John-A-Chen/Solid-Connections/Documentation/Diagrams/diagram-hero-render-red-enclosure.png

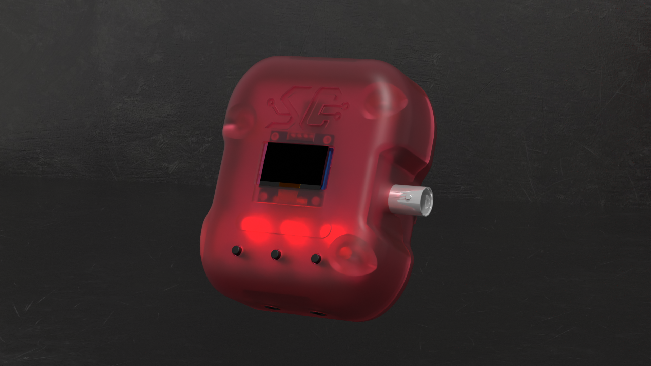
Documentation/Diagrams/diagram-hero-render-red-enclosure.png
