John-A-Chen/Solid-Connections/Documentation/Diagrams/diagram-system-block-v1.png

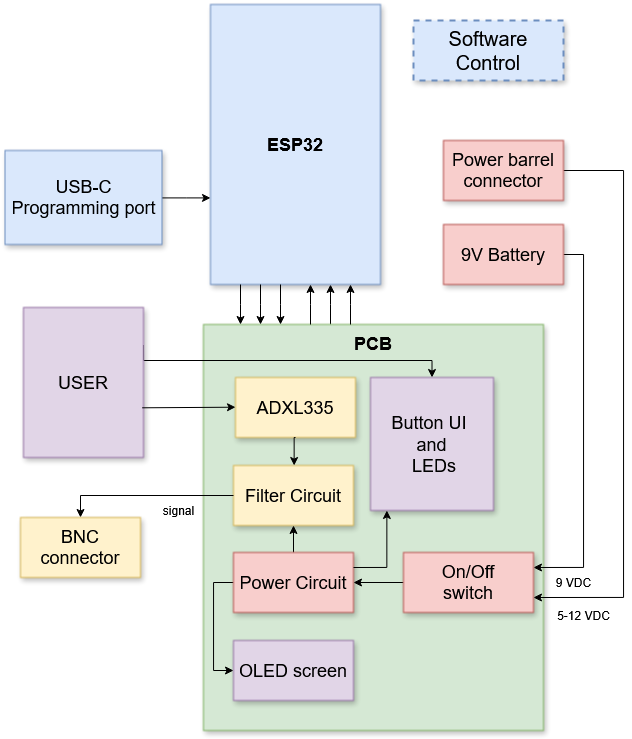
Documentation/Diagrams/diagram-system-block-v1.png
