John-A-Chen/Solid-Connections/Documentation/Images/flowchart-development-process.png

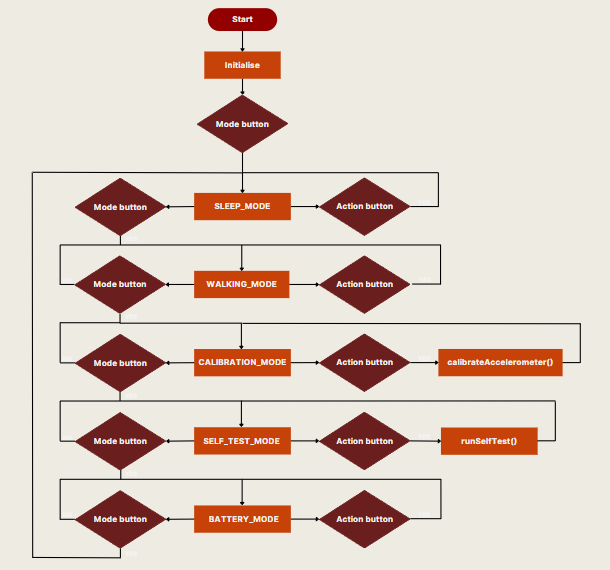
Documentation/Images/flowchart-development-process.png
