John-A-Chen/Solid-Connections/Documentation/Images/photo-device-in-hand-front-view-01.jpg

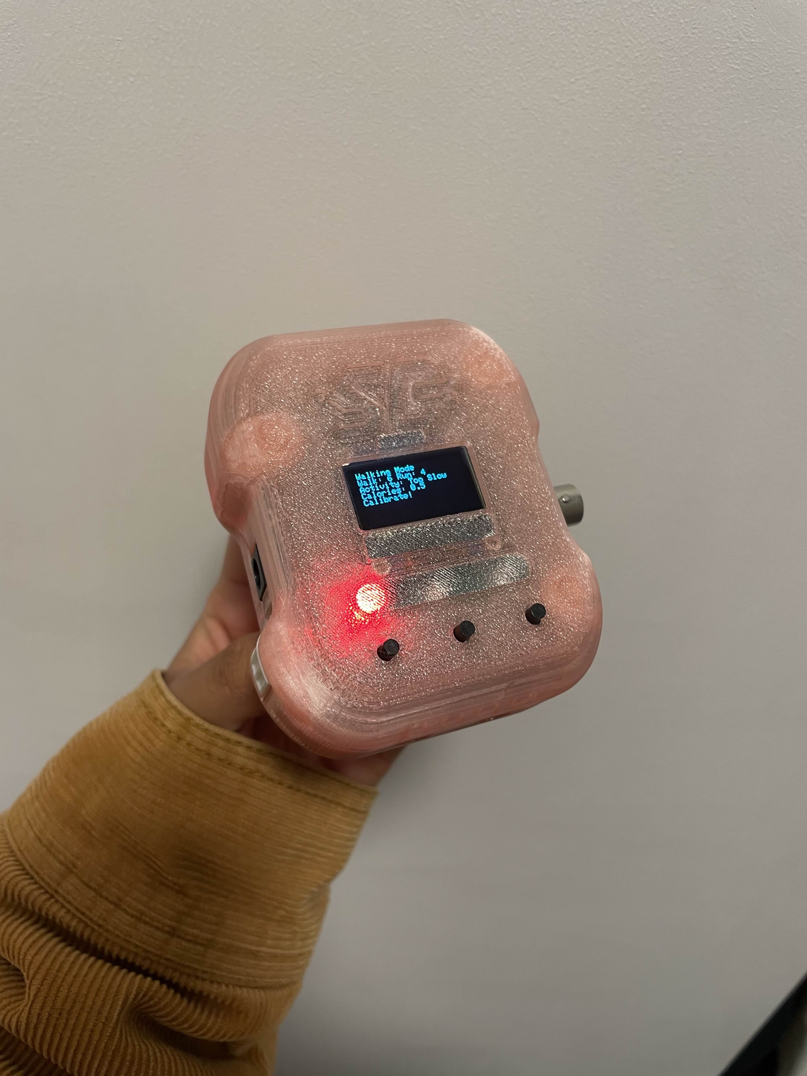
Documentation/Images/photo-device-in-hand-front-view-01.jpg
