John-A-Chen/Solid-Connections/Documentation/Images/photo-device-in-hand-front-view-03.jpg

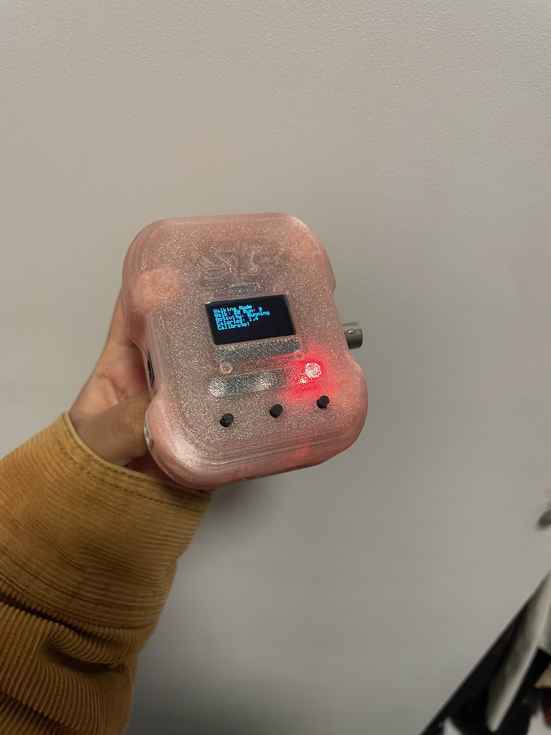
Documentation/Images/photo-device-in-hand-front-view-03.jpg
