John-A-Chen/Solid-Connections/Documentation/Images/photo-device-weight-on-scale.jpg

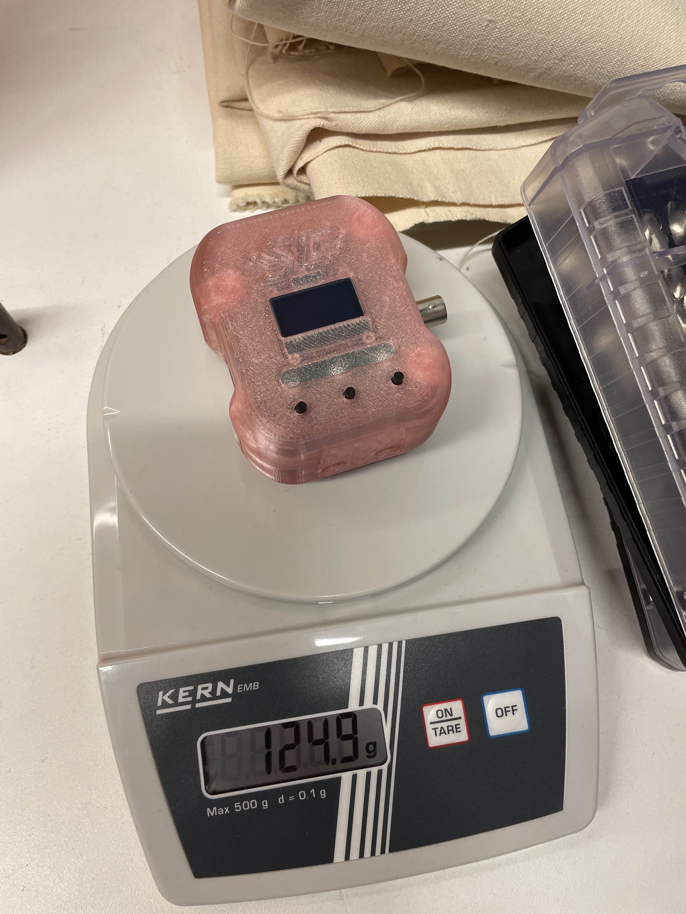
Documentation/Images/photo-device-weight-on-scale.jpg
