John-A-Chen/Solid-Connections/Documentation/Images/photo-device-worn-on-shirt.jpg

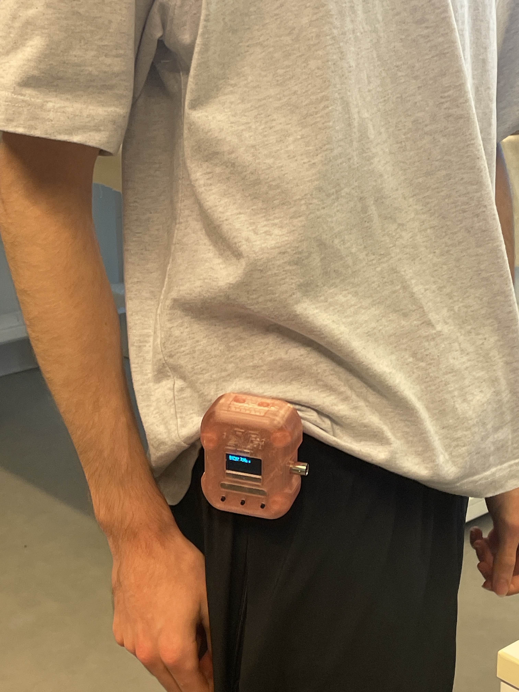
Documentation/Images/photo-device-worn-on-shirt.jpg
