John-A-Chen/Solid-Connections/Documentation/Images/photo-enclosure-front-angle-01.jpg

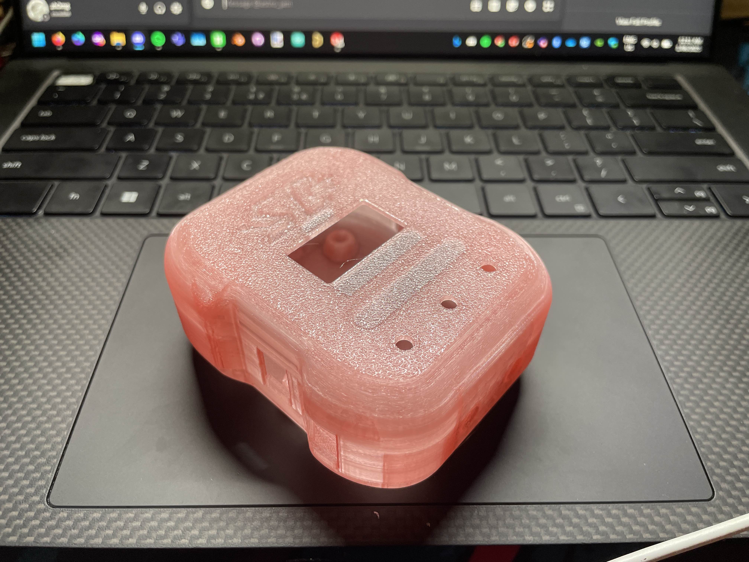
Documentation/Images/photo-enclosure-front-angle-01.jpg
