John-A-Chen/Solid-Connections/Documentation/Images/photo-enclosure-front-view-01.jpg

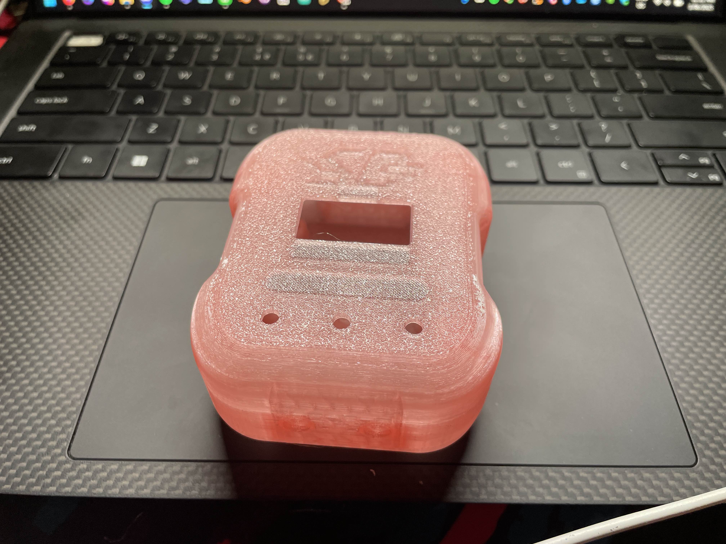
Documentation/Images/photo-enclosure-front-view-01.jpg
