John-A-Chen/Solid-Connections/Documentation/Images/photo-enclosure-side-view-01.jpg

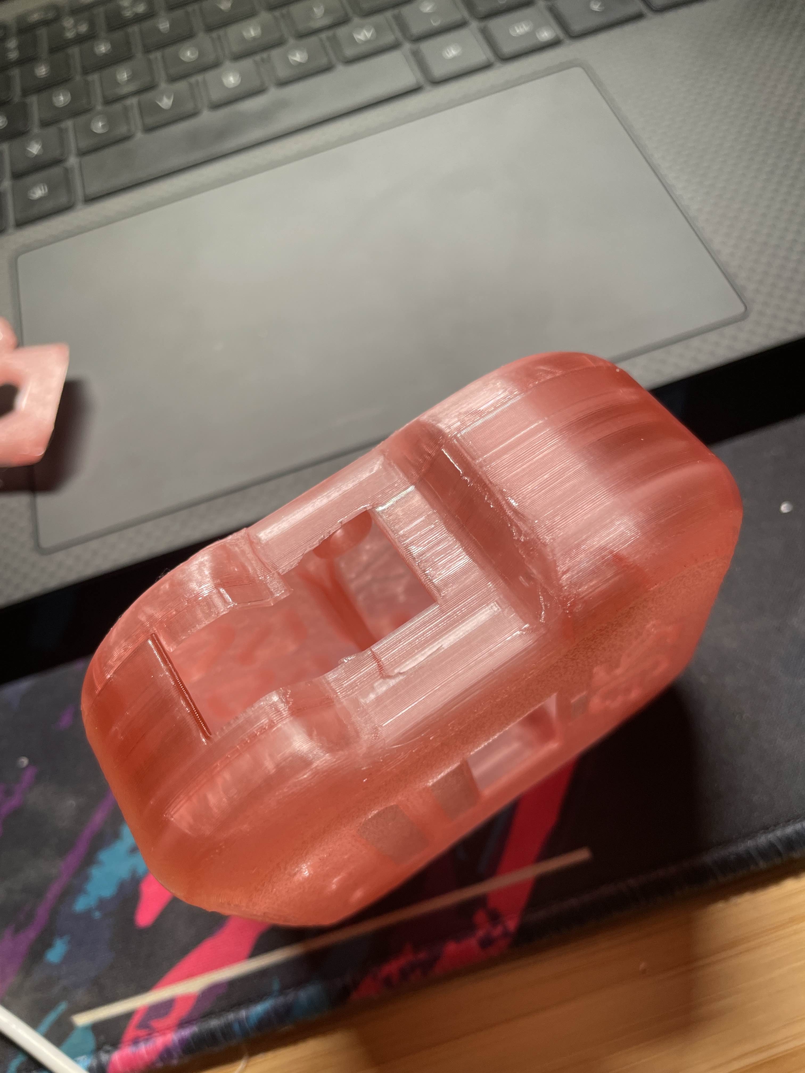
Documentation/Images/photo-enclosure-side-view-01.jpg
