John-A-Chen/Solid-Connections/Documentation/Images/photo-oled-module-on-desk.jpg

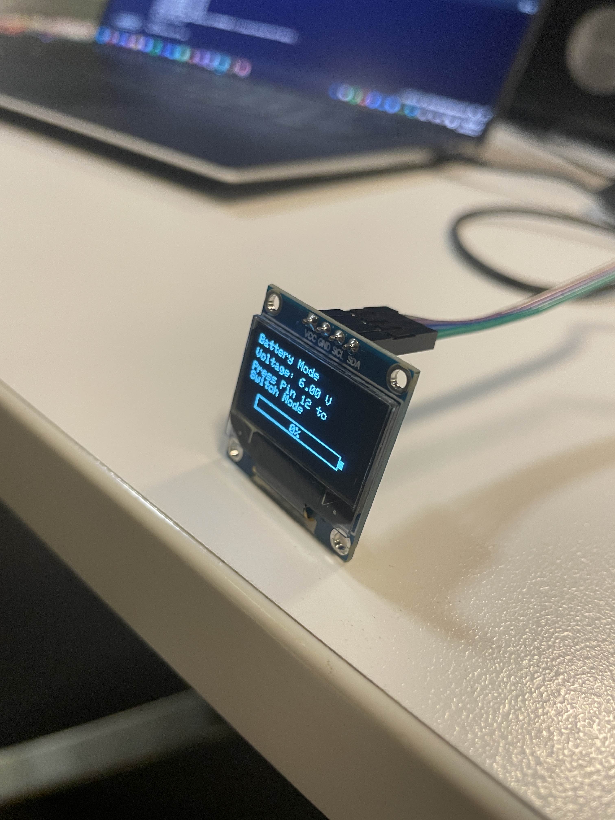
Documentation/Images/photo-oled-module-on-desk.jpg
