John-A-Chen/Solid-Connections/Documentation/Images/photo-pcb-and-oled-module-on-laptop.jpg

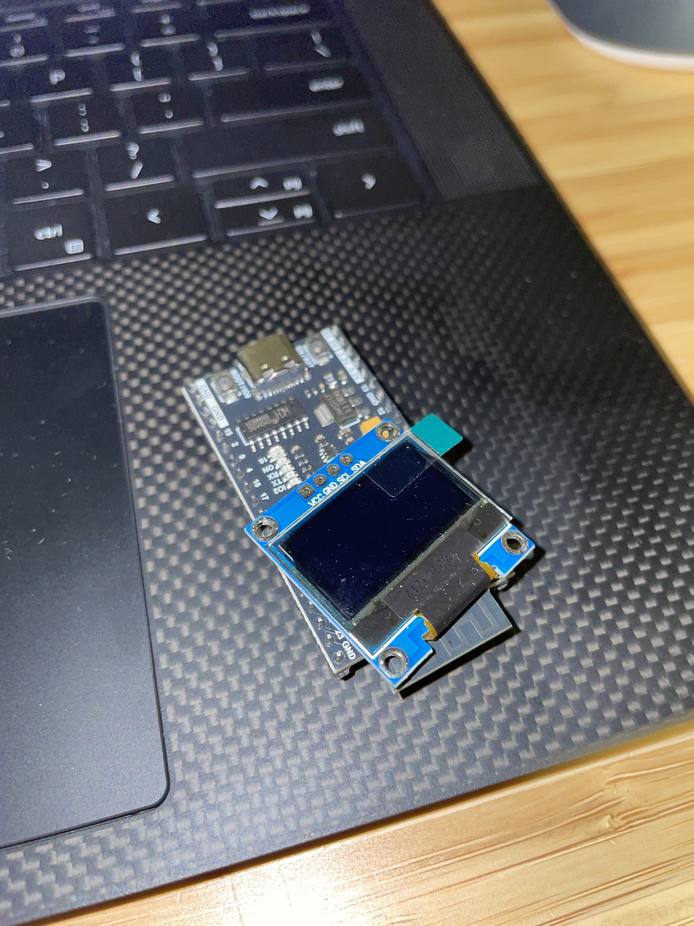
Documentation/Images/photo-pcb-and-oled-module-on-laptop.jpg
