John-A-Chen/Solid-Connections/Documentation/Images/photo-pcb-bare-back-view-01.jpg

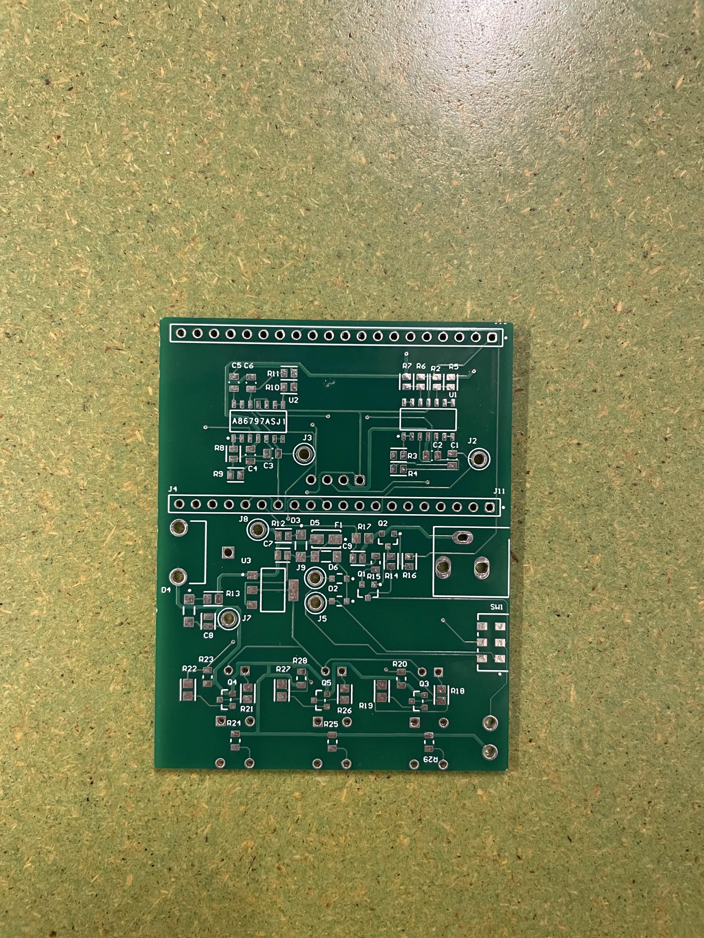
Documentation/Images/photo-pcb-bare-back-view-01.jpg
