John-A-Chen/Solid-Connections/Documentation/Images/photo-pcb-bare-back-view-02.jpg

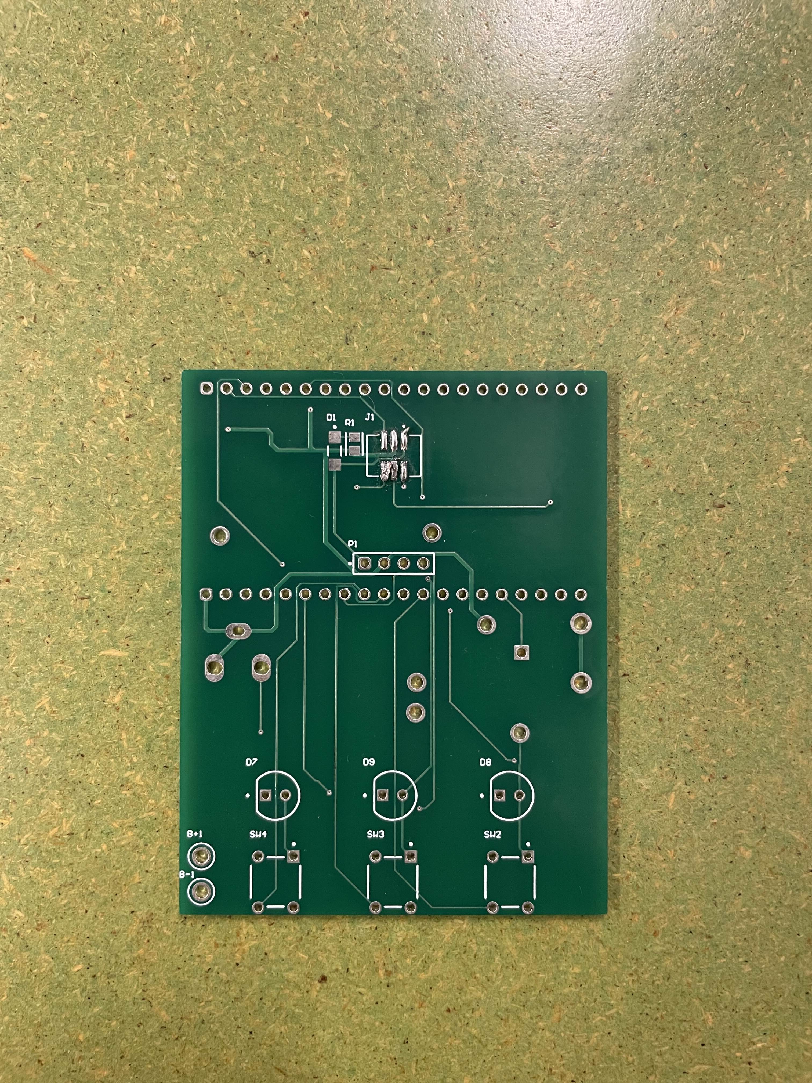
Documentation/Images/photo-pcb-bare-back-view-02.jpg
