John-A-Chen/Solid-Connections/Documentation/Images/photo-pcb-bare-front-view-01.jpg

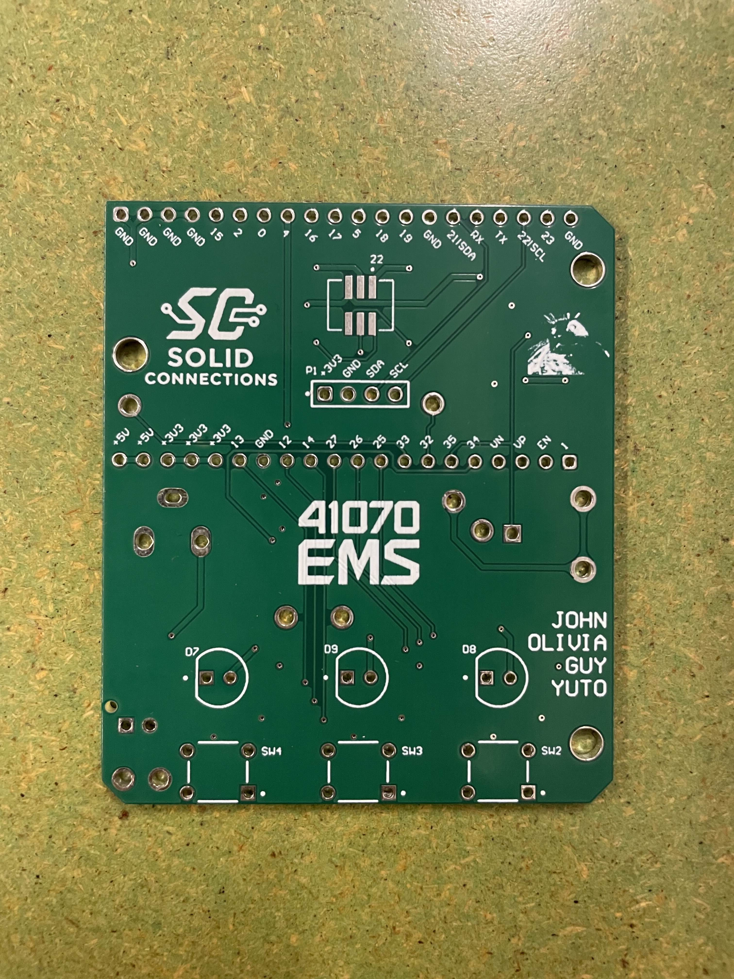
Documentation/Images/photo-pcb-bare-front-view-01.jpg
