John-A-Chen/Solid-Connections/Documentation/Images/photo-pcb-front-with-oled.jpg

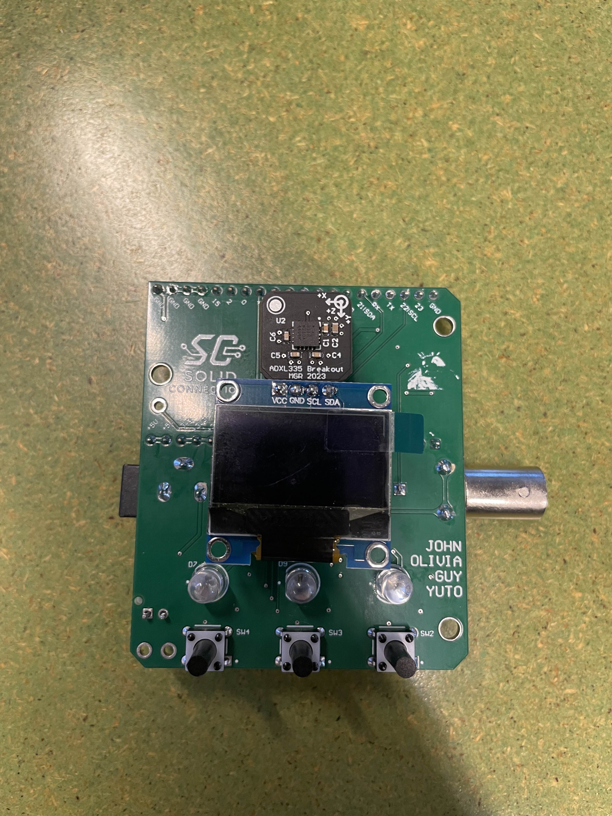
Documentation/Images/photo-pcb-front-with-oled.jpg
