John-A-Chen/Solid-Connections/Documentation/Images/photo-team-member-portrait-01.jpg

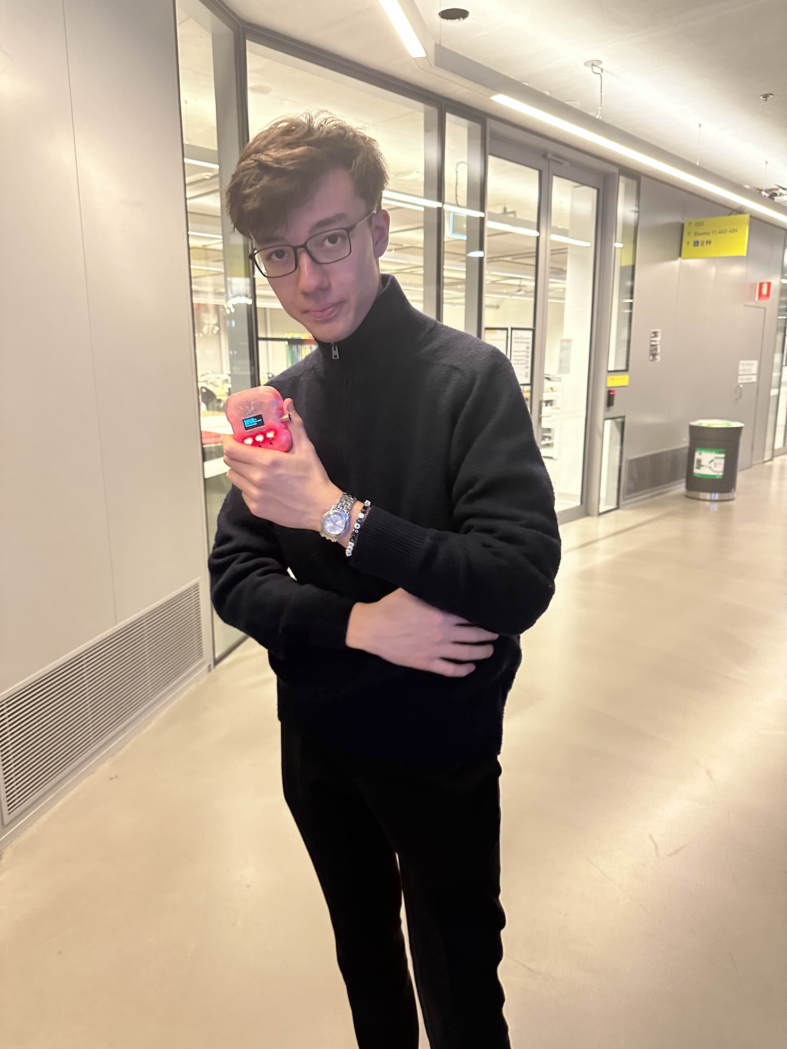
Documentation/Images/photo-team-member-portrait-01.jpg
