John-A-Chen/Solid-Connections/Documentation/Images/photo-team-member-portrait-02.jpg

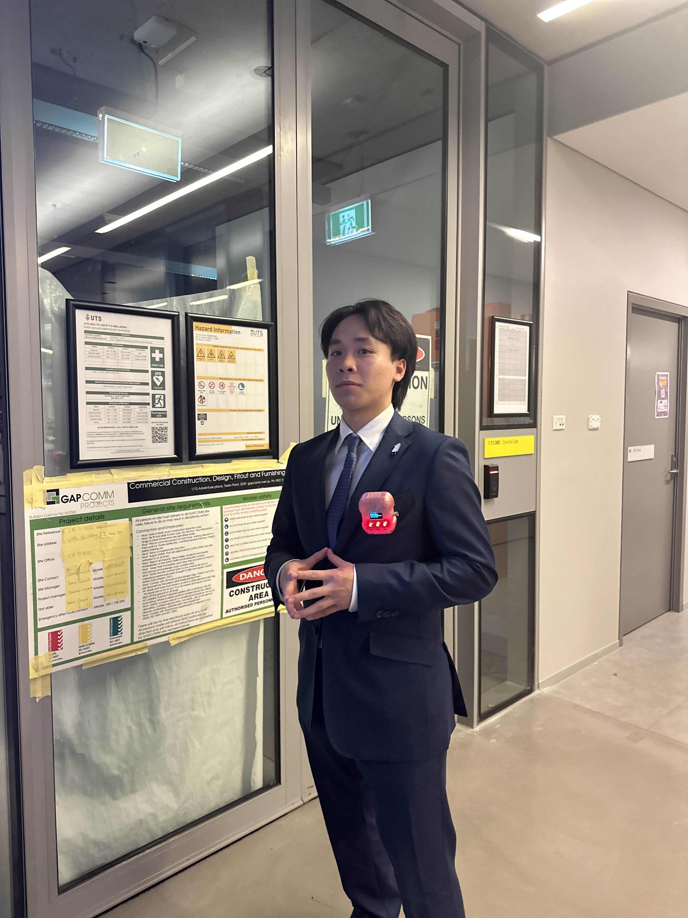
Documentation/Images/photo-team-member-portrait-02.jpg
