John-A-Chen/Solid-Connections/Documentation/Images/reference-tamagotchi-style.png

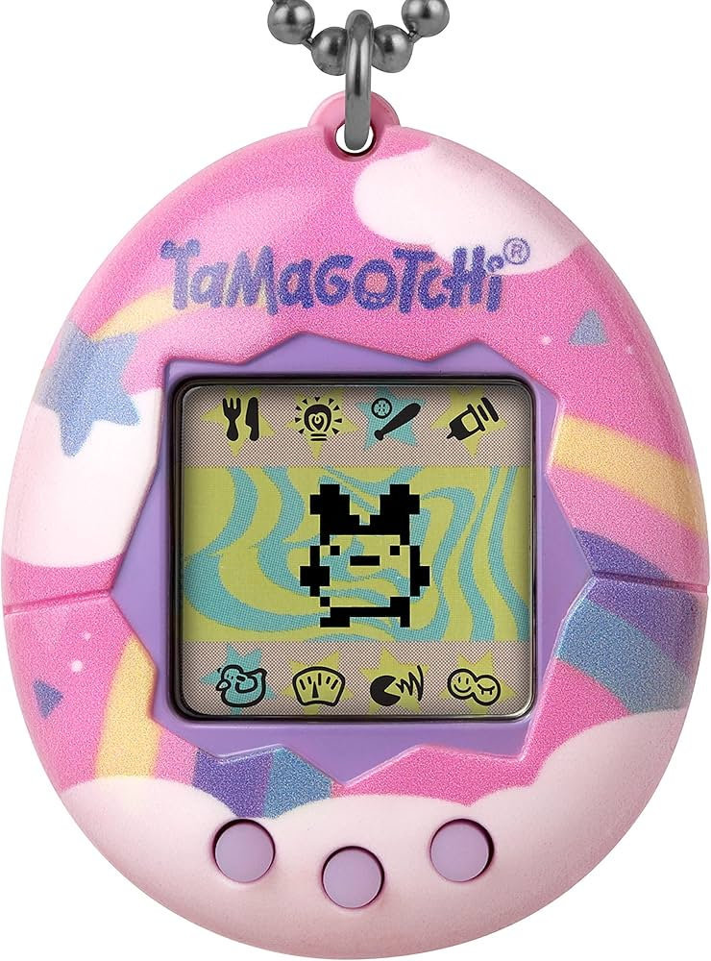
Documentation/Images/reference-tamagotchi-style.png
