John-A-Chen/Solid-Connections/Documentation/Images/render-enclosure-bottom-view.png

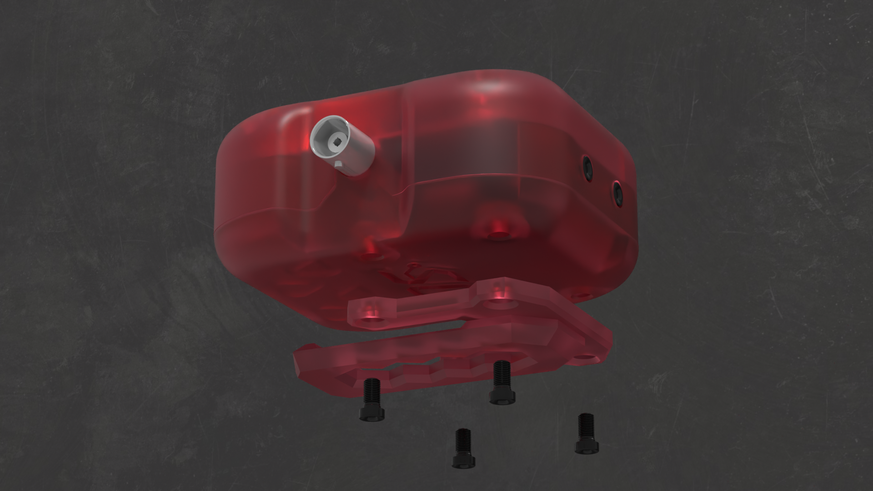
Documentation/Images/render-enclosure-bottom-view.png
