John-A-Chen/Solid-Connections/Documentation/Images/render-enclosure-open-with-pcb.png

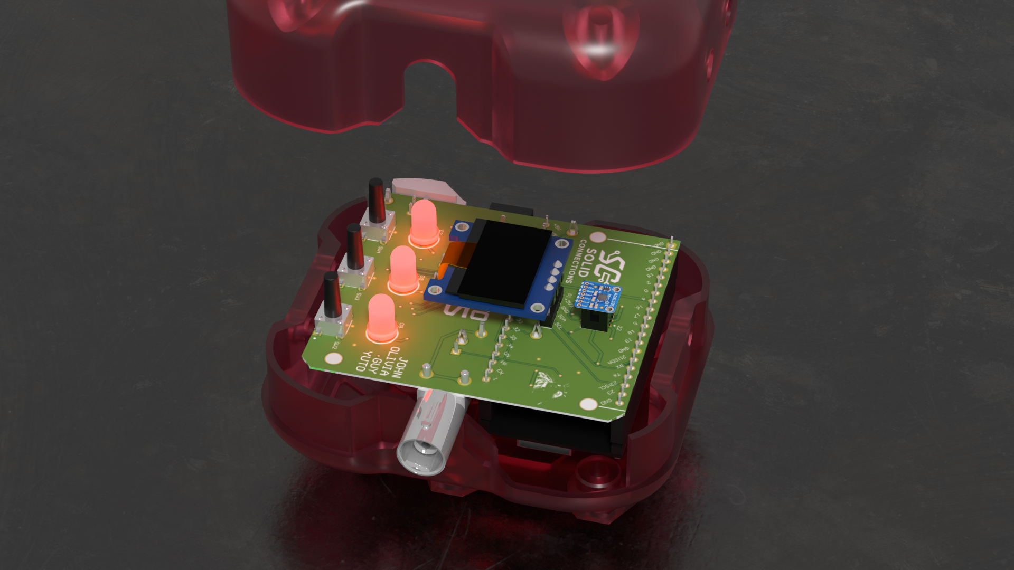
Documentation/Images/render-enclosure-open-with-pcb.png
