John-A-Chen/Solid-Connections/Documentation/Images/render-pcb-oled-closeup-01.png

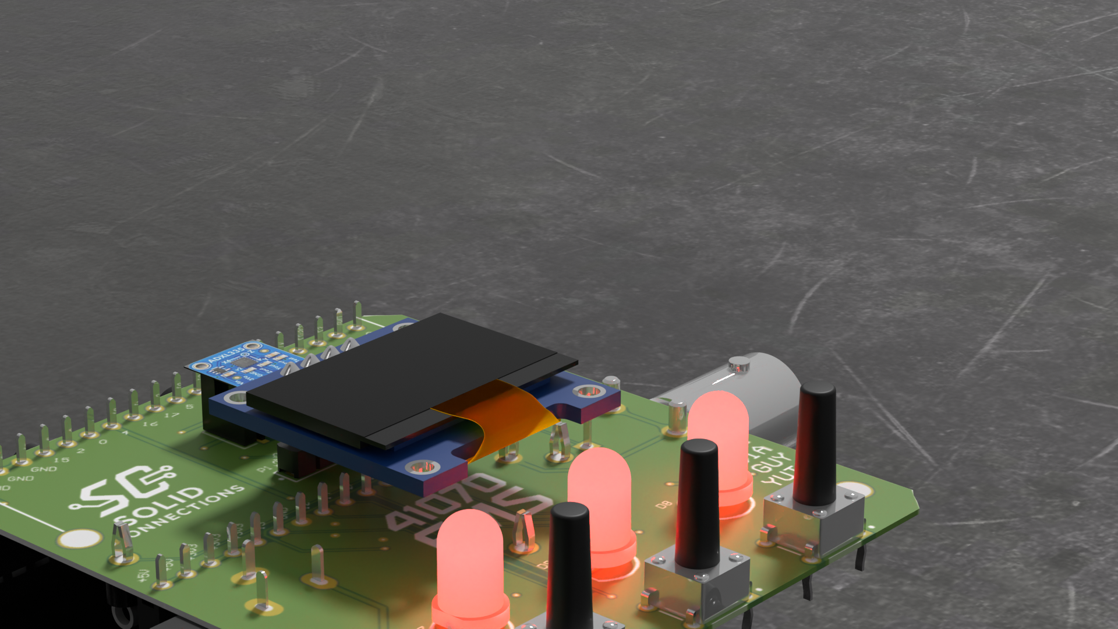
Documentation/Images/render-pcb-oled-closeup-01.png
