John-A-Chen/Solid-Connections/Documentation/Images/render-pcb-with-barrel-jack-angle-01.png

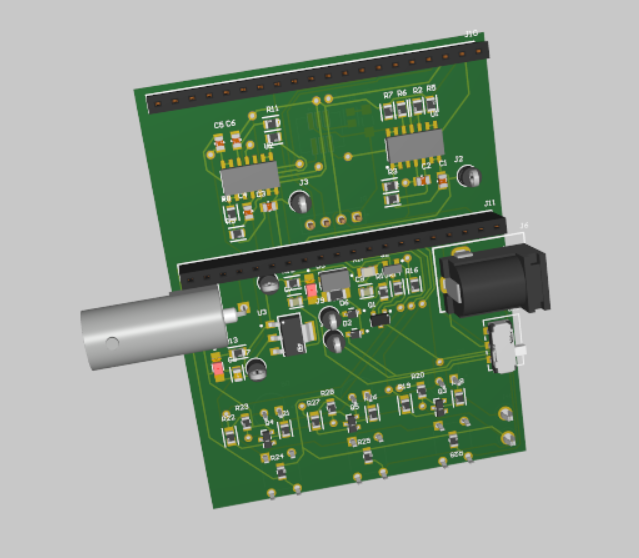
Documentation/Images/render-pcb-with-barrel-jack-angle-01.png
