John-A-Chen/Solid-Connections/Documentation/Images/render-pcb-with-controls-angle-02.png

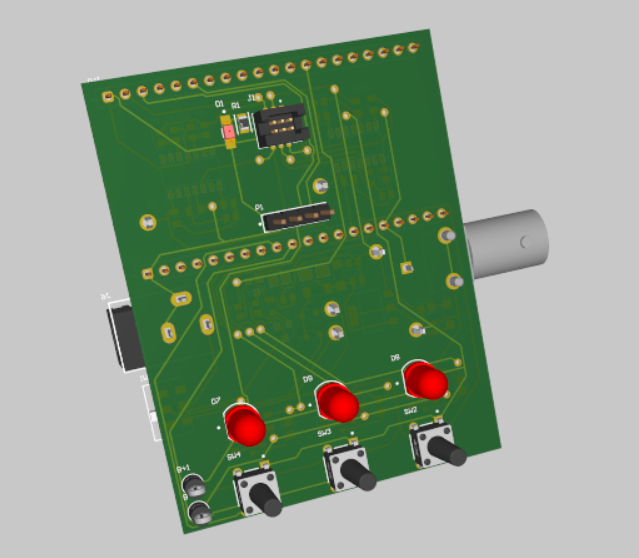
Documentation/Images/render-pcb-with-controls-angle-02.png
