John-A-Chen/Solid-Connections/Documentation/Images/render-purple-enclosure-front.png

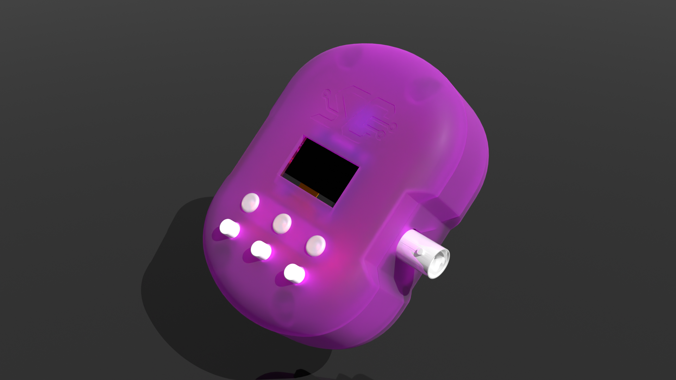
Documentation/Images/render-purple-enclosure-front.png
