John-A-Chen/Solid-Connections/Documentation/Images/render-side-stackup-view.png

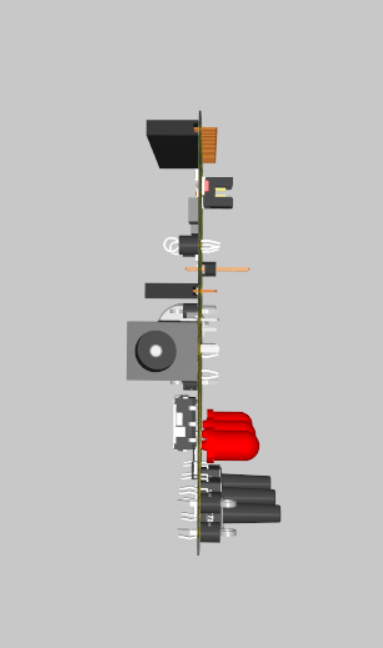
Documentation/Images/render-side-stackup-view.png
