John-A-Chen/Solid-Connections/Documentation/Images/render-technical-drawing-sheet.png

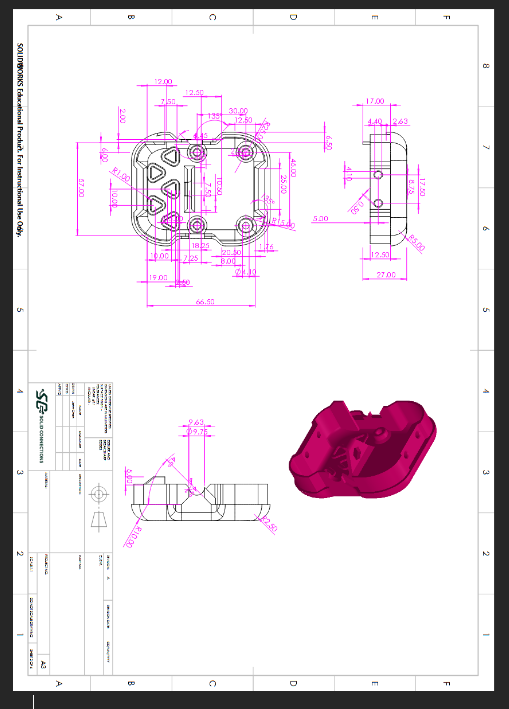
Documentation/Images/render-technical-drawing-sheet.png
