John-A-Chen/Solid-Connections/Documentation/Images/render-transparent-enclosure-cutaway-01.png

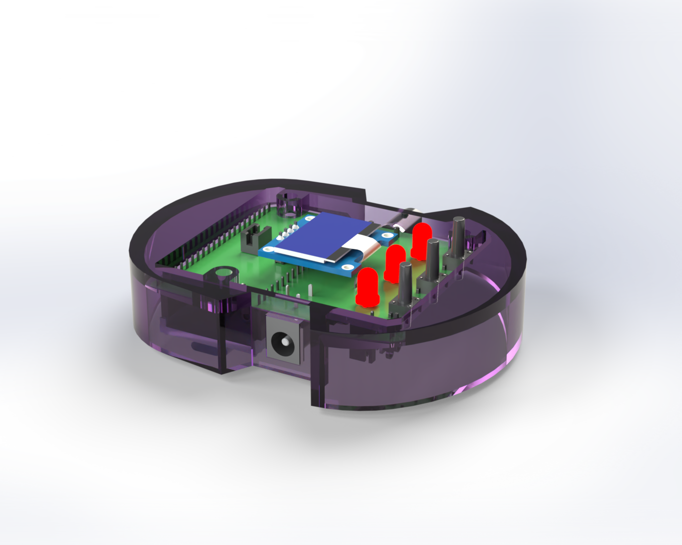
Documentation/Images/render-transparent-enclosure-cutaway-01.png
