John-A-Chen/Solid-Connections/Documentation/Images/render-transparent-enclosure-cutaway-02.png

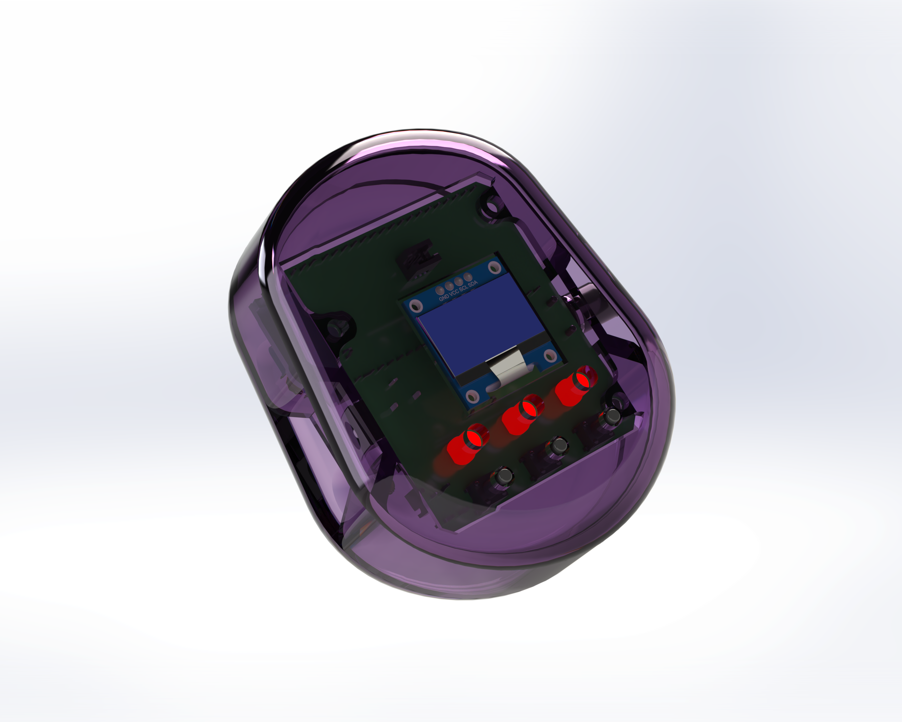
Documentation/Images/render-transparent-enclosure-cutaway-02.png
