John-A-Chen/Solid-Connections/Documentation/Images/photo-printed-parts-set-01.jpg

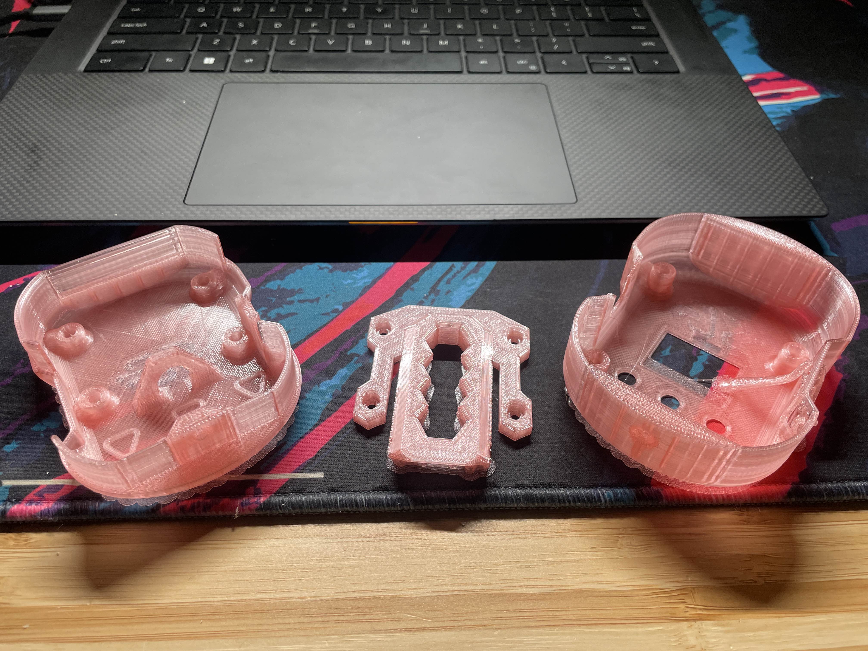
Documentation/Images/photo-printed-parts-set-01.jpg
