John-A-Chen/Solid-Connections/Documentation/Images/photo-printed-parts-set-02.jpg

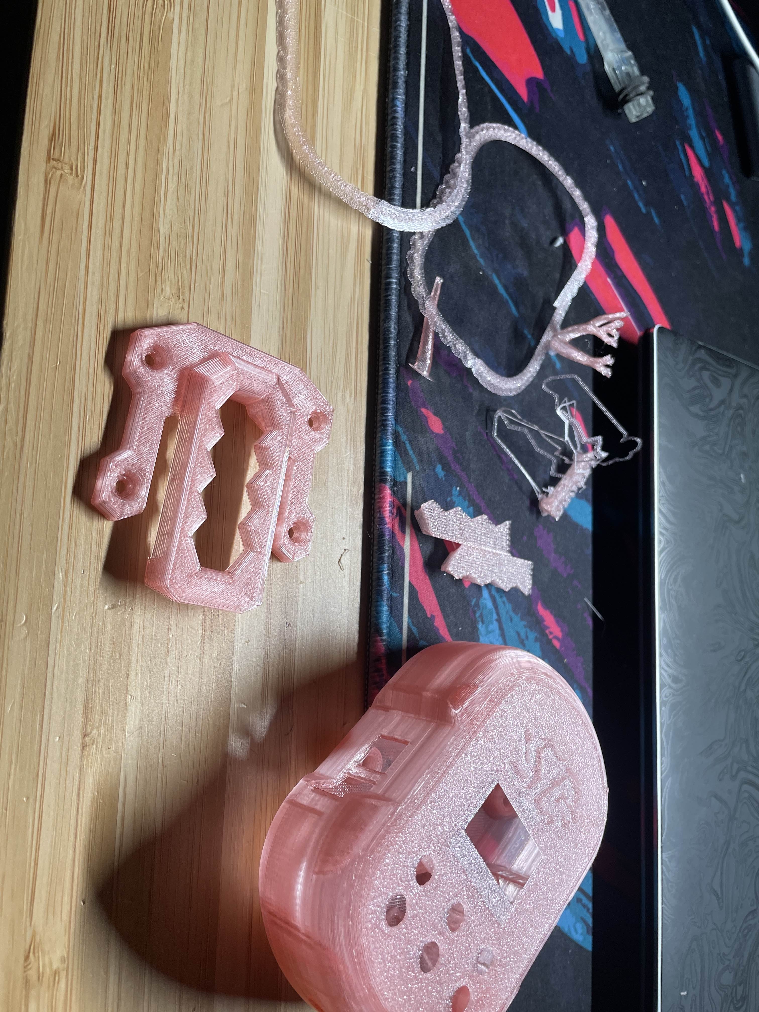
Documentation/Images/photo-printed-parts-set-02.jpg
