John-A-Chen/Solid-Connections/CAD/Assemblies/electronics package.SLDASM

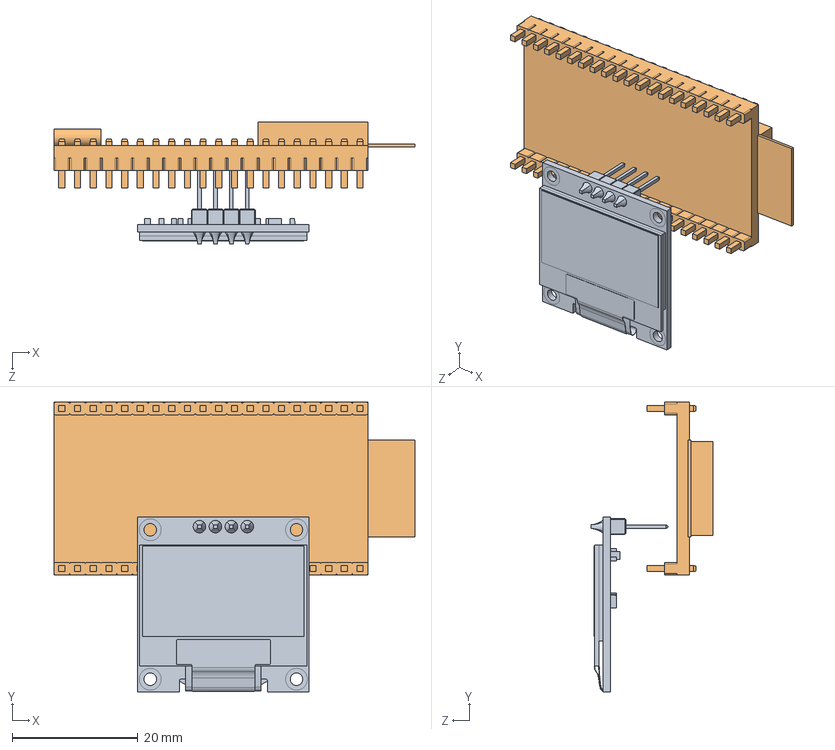
[picture p84: CAD file, 2026-03-31]
CAD/Assemblies/electronics package.SLDASM
57.5 x 46.1 x 19.5 mm
esp32
OLED TFT 0.96 inch 64x128 monochrome
