John-A-Chen/Solid-Connections/CAD/Print_Exports/clip2.3mf

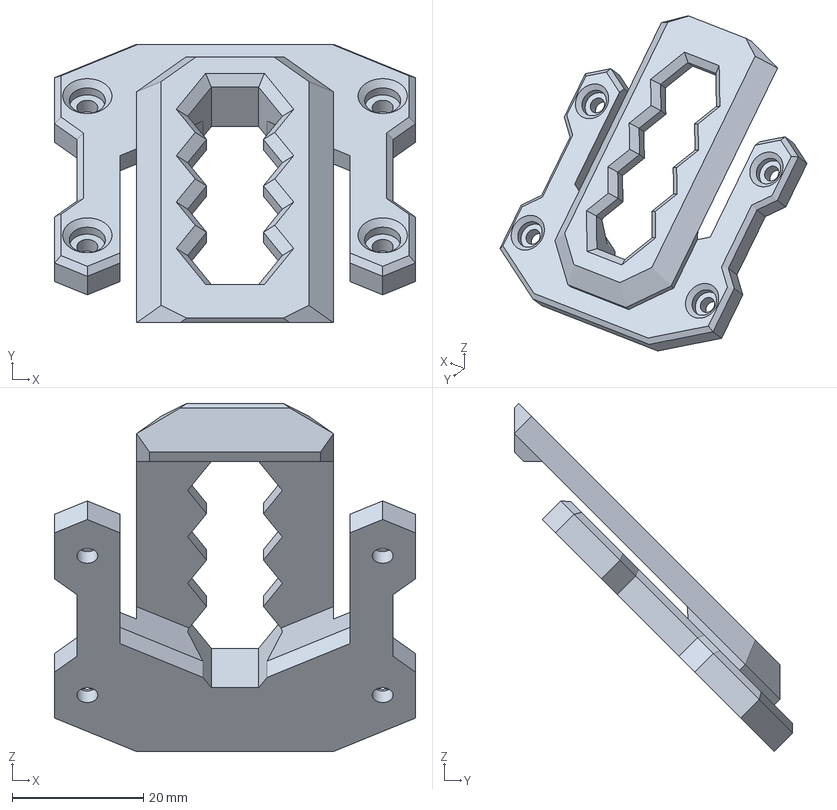
[picture p100: CAD file, 2026-02-22]
CAD/Print_Exports/clip2.3mf
55.0 x 42.4 x 53.0 mm
