John-A-Chen/Solid-Connections/Electronics/Reference_Models/esp32.SLDPRT

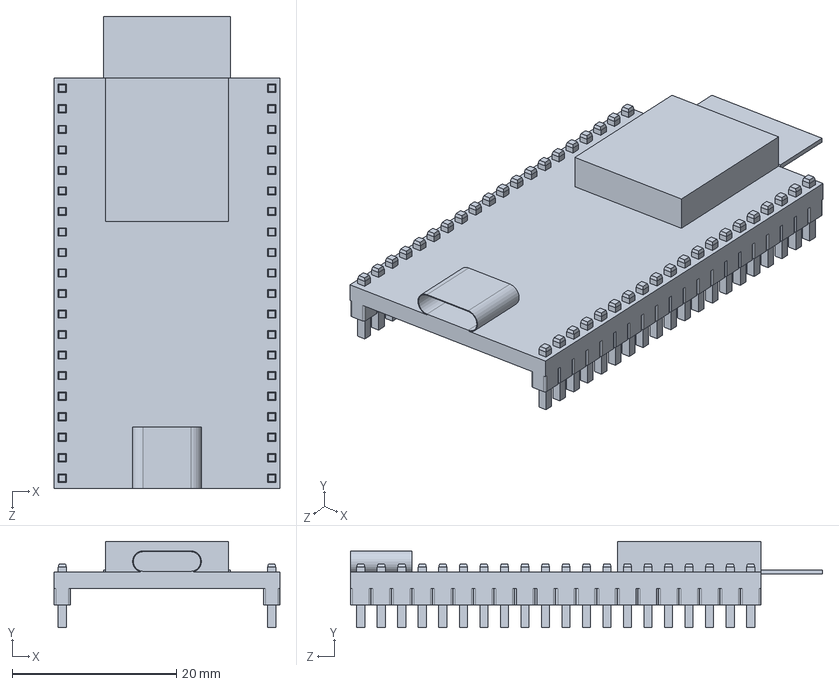
[picture p101: CAD file, 2026-02-22]
Electronics/Reference_Models/esp32.SLDPRT
27.5 x 10.5 x 57.5 mm
