John-A-Chen/Solid-Connections/CAD/Components/diffuser.STEP

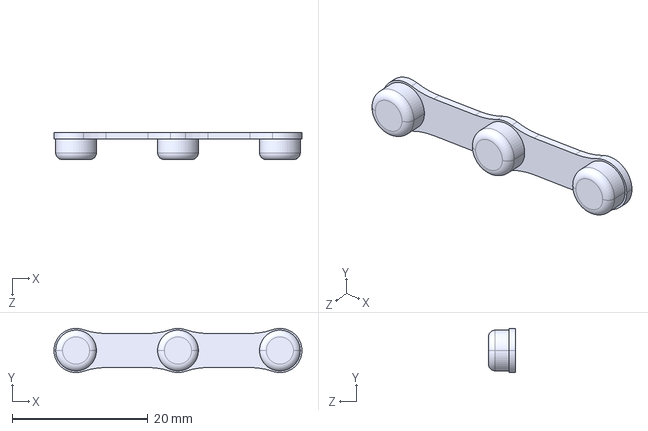
[picture p102: CAD file, 2026-02-22]
CAD/Components/diffuser.STEP
36.5 x 6.50 x 4.00 mm
