John-A-Chen/Solid-Connections/CAD/Print_Exports/switchcover2.3mf

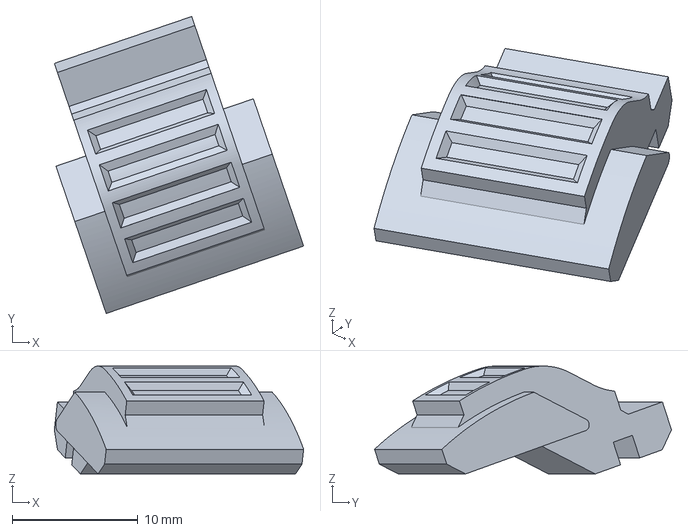
[picture p103: CAD file, 2026-02-22]
CAD/Print_Exports/switchcover2.3mf
19.8 x 23.6 x 8.58 mm
