John-A-Chen/Solid-Connections/CAD/Components/shellback6.STEP

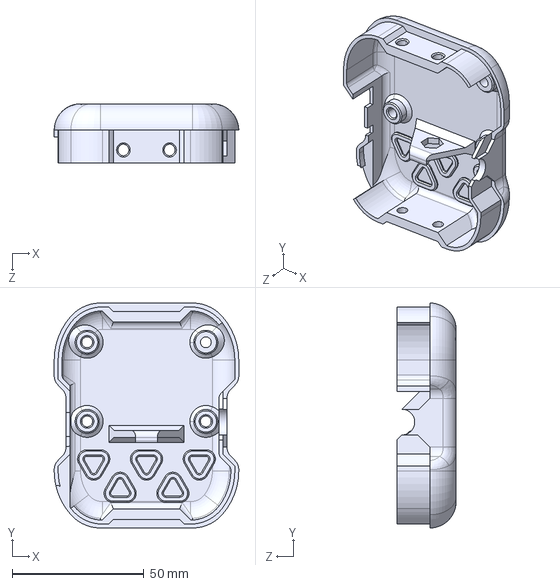
[picture p104: CAD file, 2026-02-22]
CAD/Components/shellback6.STEP
70.0 x 85.3 x 22.5 mm
