John-A-Chen/Solid-Connections/CAD/Print_Exports/shellback.3mf

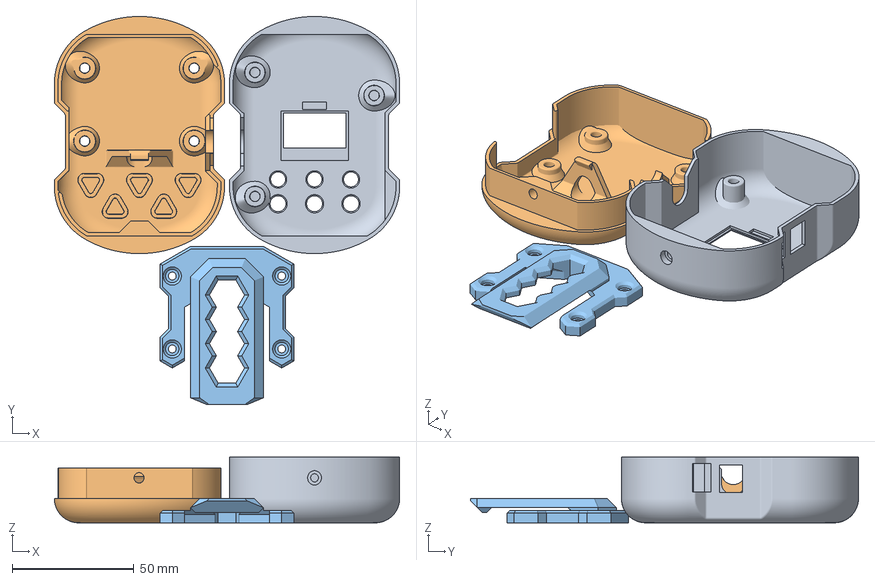
[picture p105: CAD file, 2026-02-22]
CAD/Print_Exports/shellback.3mf
142.0 x 159.6 x 27.0 mm
shellfront.STEP
shellback.STEP
clip2.STEP
