John-A-Chen/Solid-Connections/CAD/Components/clip3.STEP

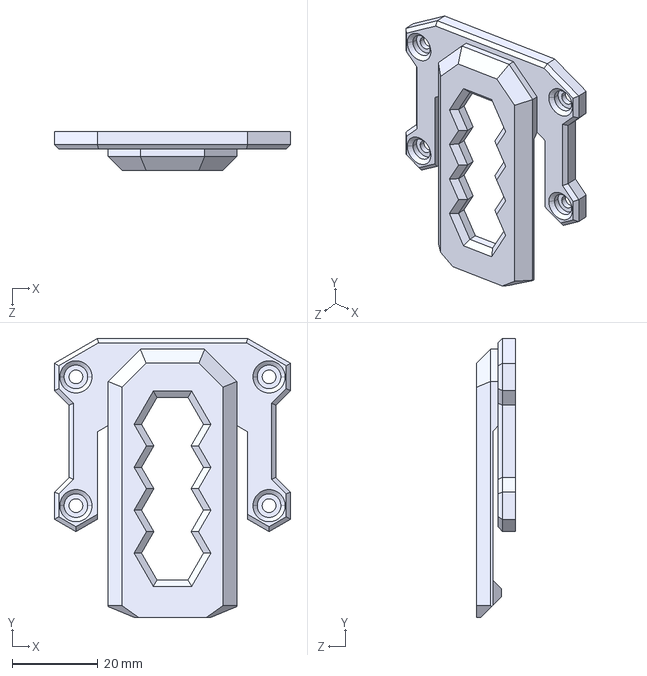
[picture p106: CAD file, 2026-02-22]
CAD/Components/clip3.STEP
55.0 x 65.0 x 9.00 mm
