John-A-Chen/Solid-Connections/CAD/Components/shell7.STEP

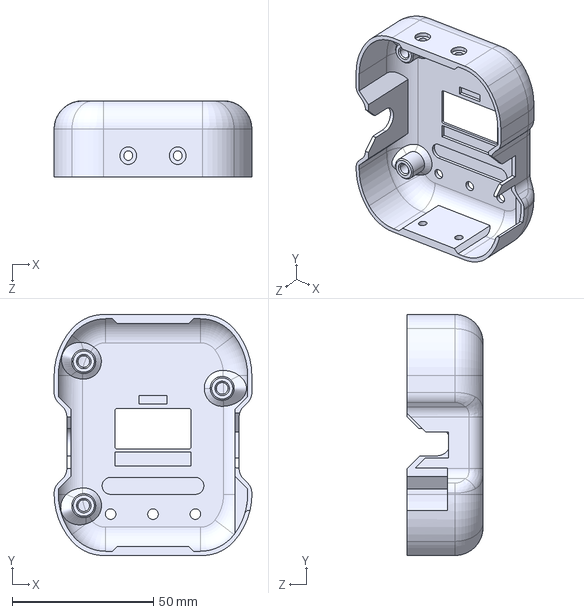
[picture p107: CAD file, 2026-02-22]
CAD/Components/shell7.STEP
70.0 x 85.3 x 27.0 mm
