John-A-Chen/Solid-Connections/CAD/Components/clear.STEP

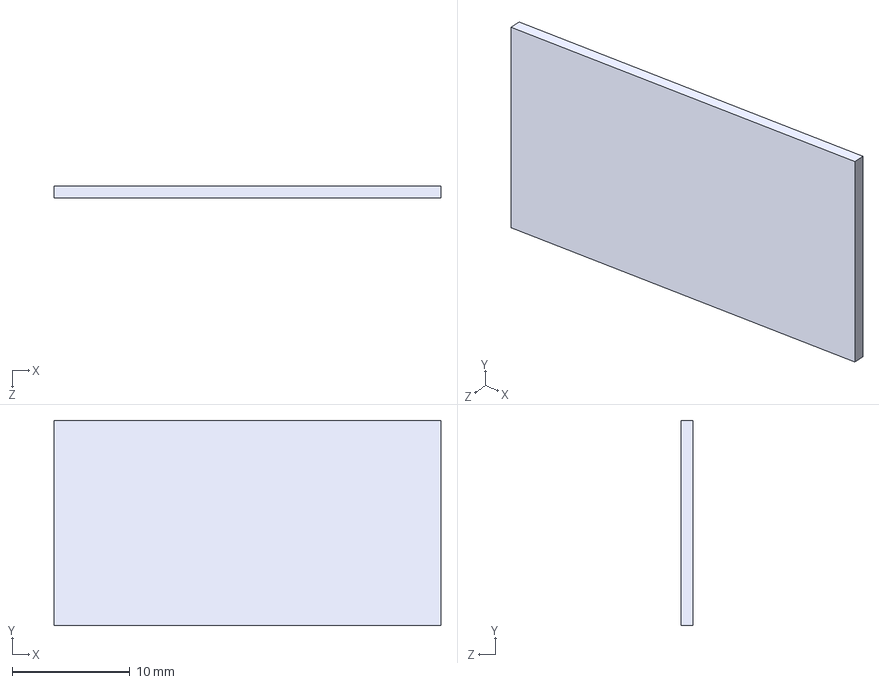
[picture p108: CAD file, 2026-02-22]
CAD/Components/clear.STEP
32.8 x 17.4 x 1.00 mm
