John-A-Chen/Solid-Connections/CAD/Components/switchcover2.STEP

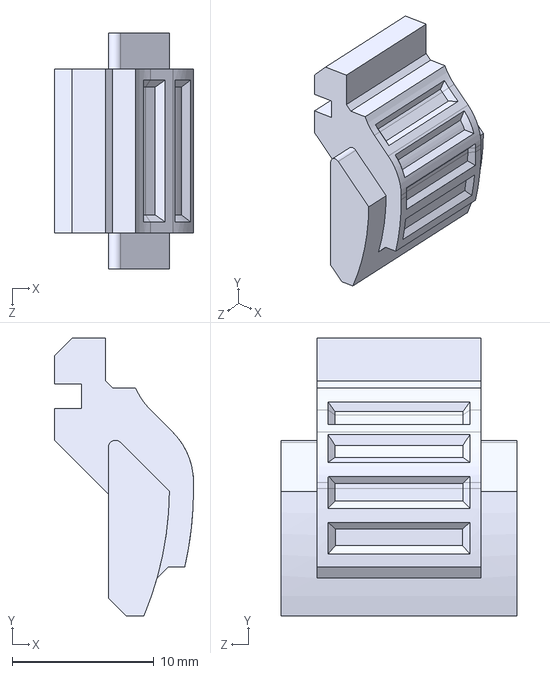
[picture p109: CAD file, 2026-02-22]
CAD/Components/switchcover2.STEP
9.80 x 19.6 x 16.6 mm
