John-A-Chen/Solid-Connections/CAD/Components/Battery_9V.SLDPRT

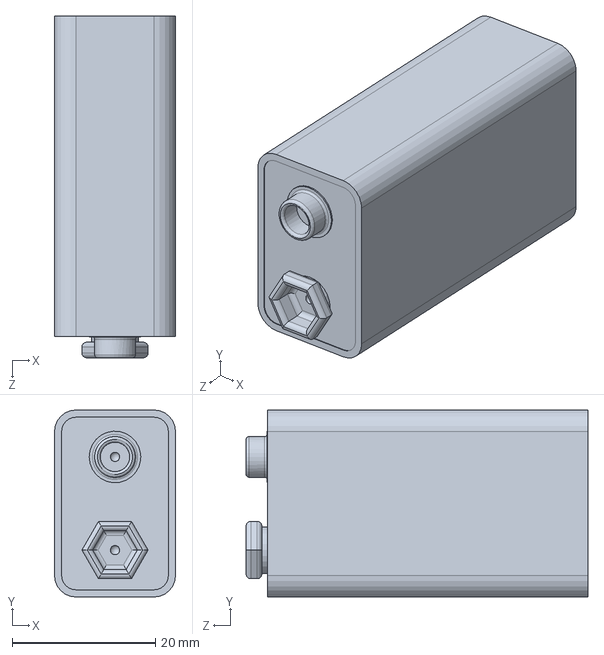
[picture p110: CAD file, 2026-02-22]
CAD/Components/Battery_9V.SLDPRT
16.9 x 26.1 x 47.7 mm
