John-A-Chen/Solid-Connections/CAD/Components/9V_BatteryAdaptor.step

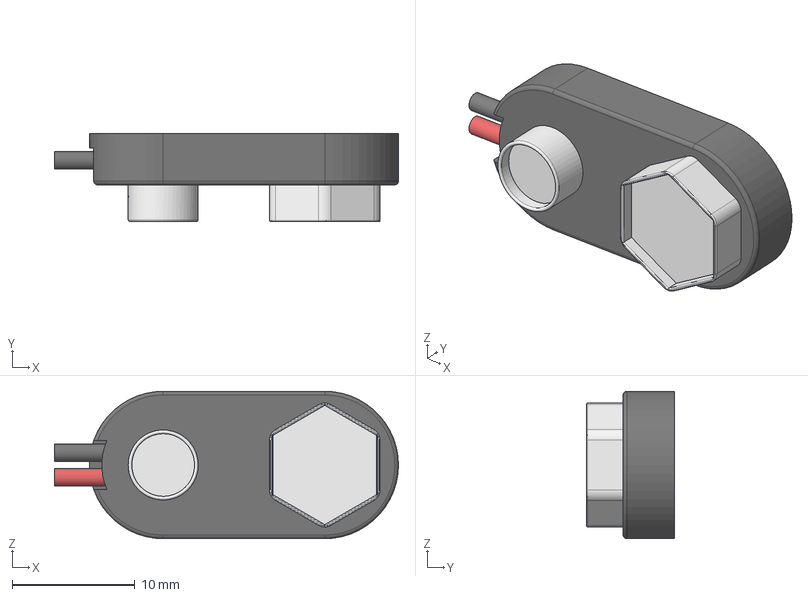
[picture p111: CAD file, 2026-02-22]
CAD/Components/9V_BatteryAdaptor.step
28.0 x 7.20 x 12.0 mm
