John-A-Chen/Solid-Connections/CAD/Components/switchcover.STEP

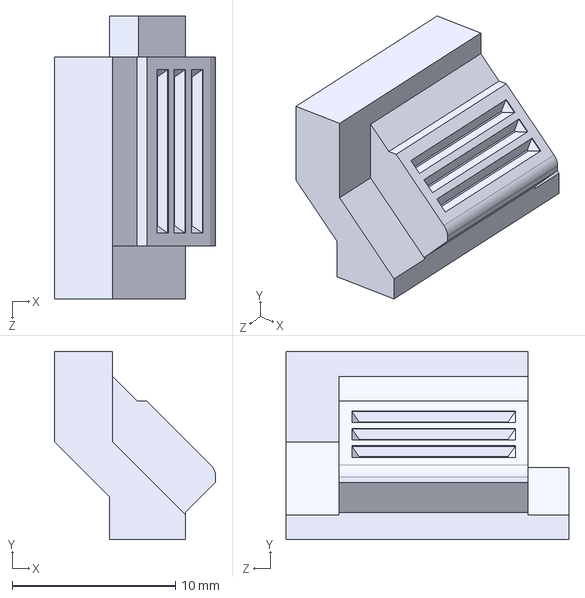
[picture p112: CAD file, 2026-02-22]
CAD/Components/switchcover.STEP
9.88 x 11.5 x 17.3 mm
