John-A-Chen/Solid-Connections/CAD/Components/oledspacer.STEP

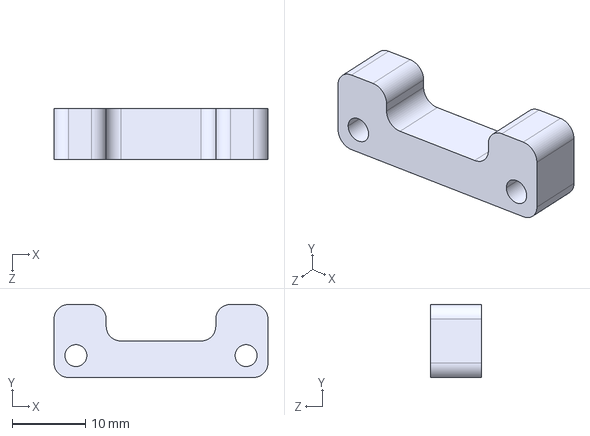
[picture p113: CAD file, 2026-02-22]
CAD/Components/oledspacer.STEP
29.3 x 10.0 x 7.00 mm
