John-A-Chen/Solid-Connections/CAD/Components/buttoncap.STEP

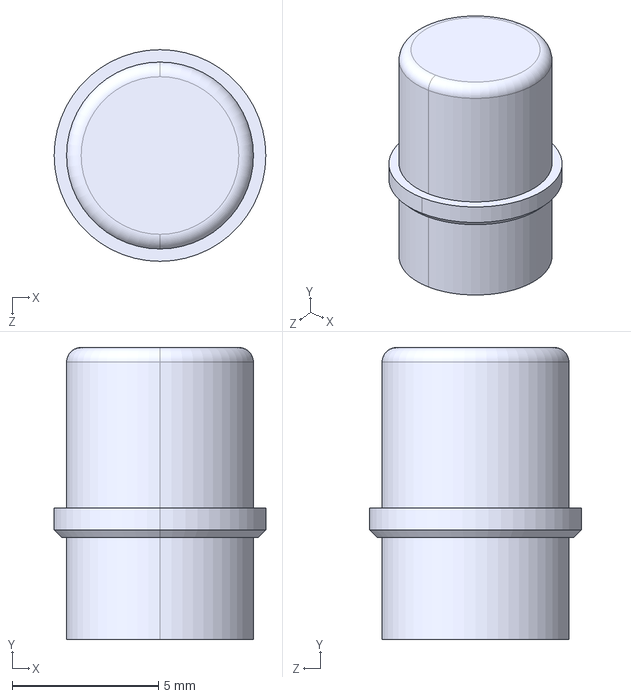
[picture p114: CAD file, 2026-02-22]
CAD/Components/buttoncap.STEP
7.25 x 10.0 x 7.25 mm
