John-A-Chen/Solid-Connections/CAD/Components/clip2.STEP

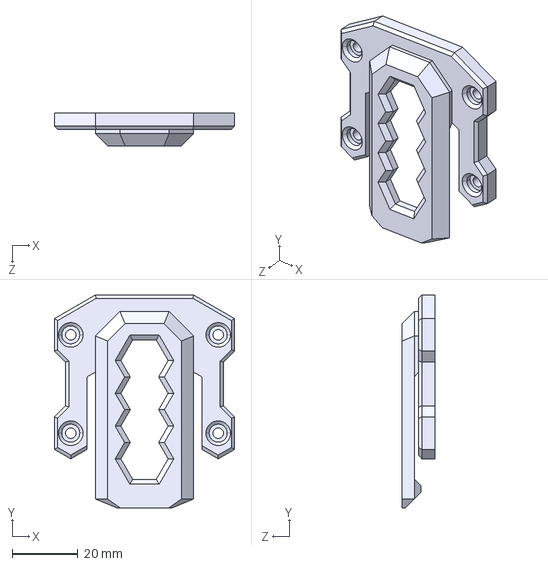
[picture p115: CAD file, 2026-02-22]
CAD/Components/clip2.STEP
55.0 x 65.0 x 10.0 mm
