John-A-Chen/Solid-Connections/CAD/Components/buttoncaps.STEP

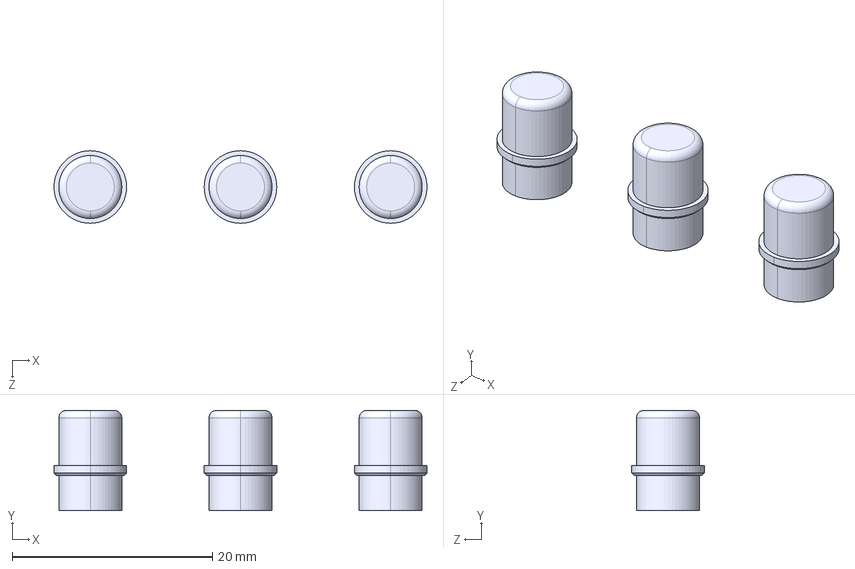
[picture p116: CAD file, 2026-02-22]
CAD/Components/buttoncaps.STEP
37.2 x 10.0 x 7.25 mm
buttoncap x 3
