John-A-Chen/Solid-Connections/CAD/Assemblies/pcb bruh 5.SLDASM

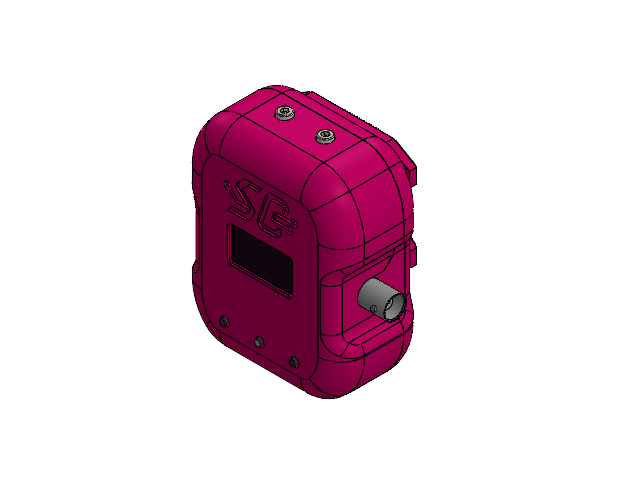
[picture p117: CAD file, 2026-03-31]
CAD/Assemblies/pcb bruh 5.SLDASM
hi
esp32
OLED TFT 0.96 inch 64x128 monochrome
switchcover2.5
9V_BatteryAdaptor
Battery_9V
clip2
Insert M3 D5 L5mm x 11
socket head cap screw_am x 11
