John-A-Chen/Solid-Connections/Documentation/Images/render-cad-exploded-assembly-purple.png

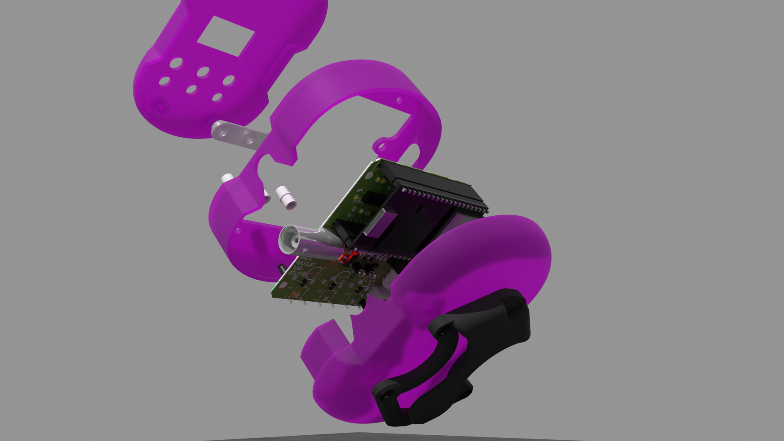
Documentation/Images/render-cad-exploded-assembly-purple.png
