John-A-Chen/Solid-Connections/Documentation/Images/render-exploded-assembly-angle-a.png

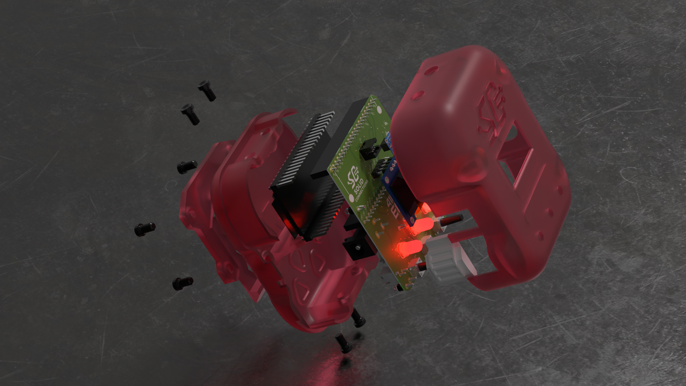
Documentation/Images/render-exploded-assembly-angle-a.png
