John-A-Chen/Solid-Connections/Documentation/Images/render-exploded-assembly-horizontal-01.png

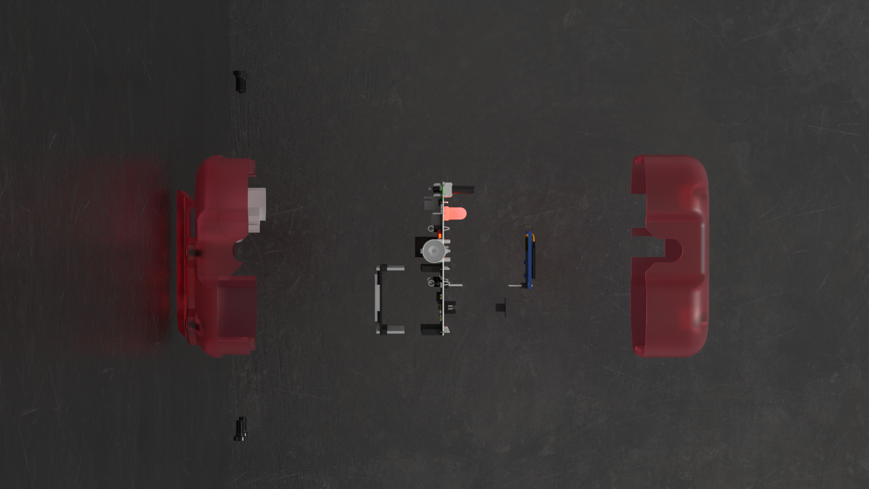
Documentation/Images/render-exploded-assembly-horizontal-01.png
