John-A-Chen/Solid-Connections/Documentation/Images/render-exploded-assembly-vertical-01.png

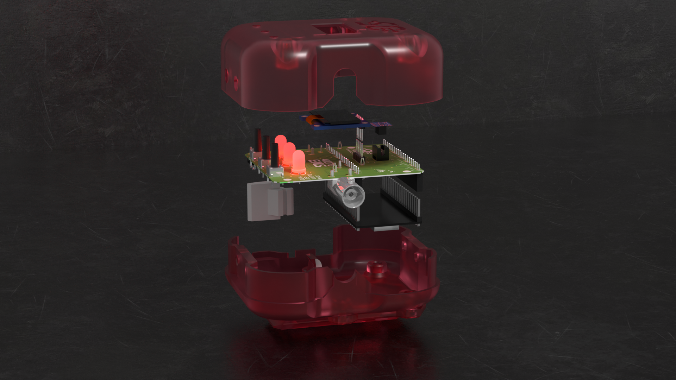
Documentation/Images/render-exploded-assembly-vertical-01.png
